wguilherme/FusionBrick/examples/rover-chassis/assembly.gif

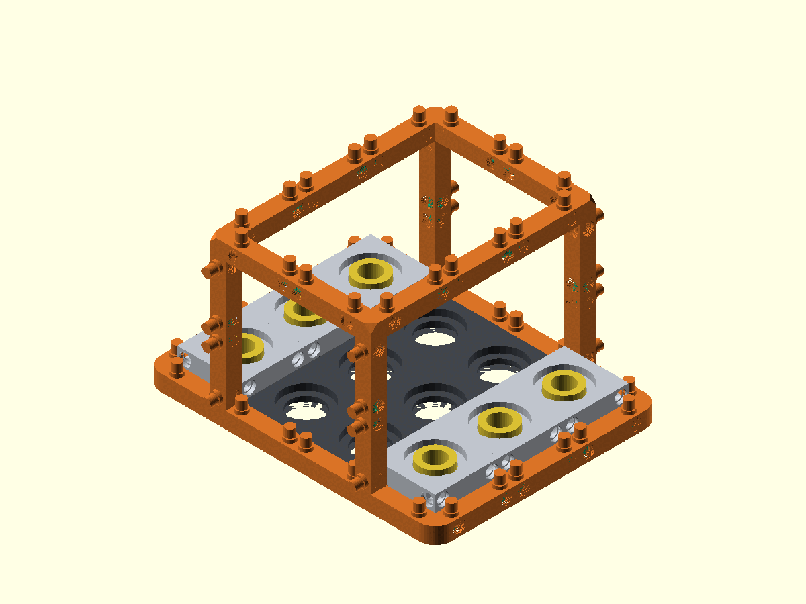
examples/rover-chassis/assembly.gif
